alexei8a/Open-Air-duinoberry/Screenshots/device_list.png

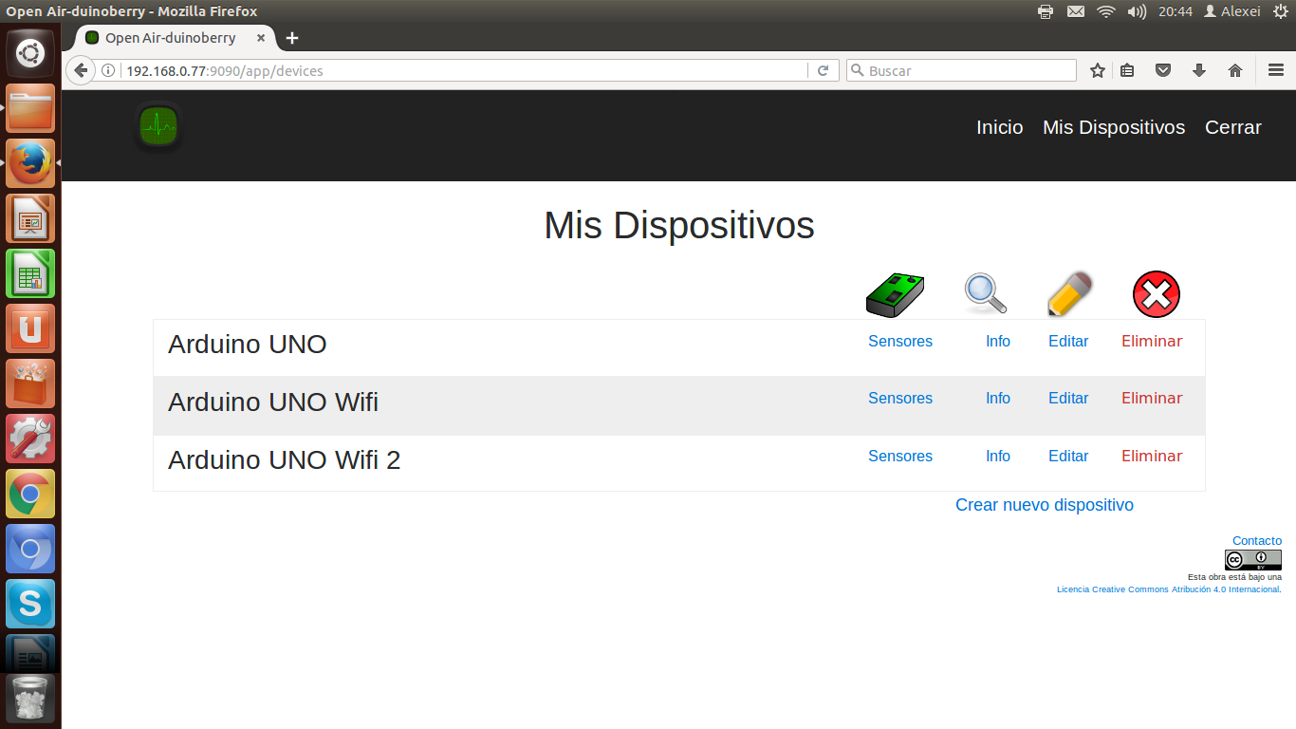
Screenshots/device_list.png
