alexei8a/Open-Air-duinoberry/Screenshots/edit_device.png

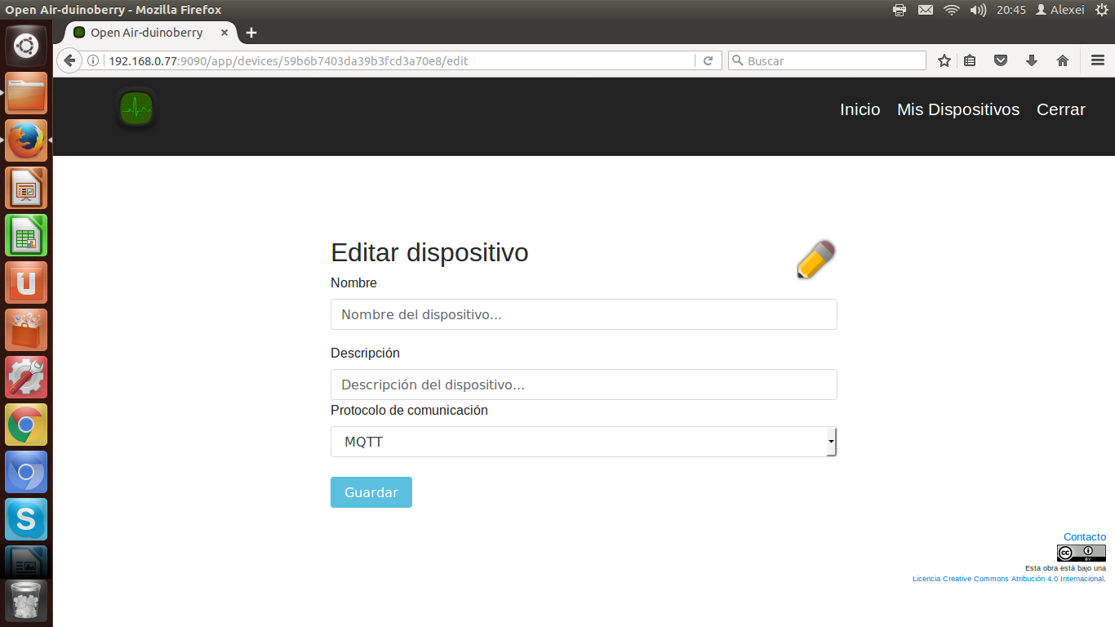
Screenshots/edit_device.png
