alexei8a/Open-Air-duinoberry/Screenshots/edit_sensor.png

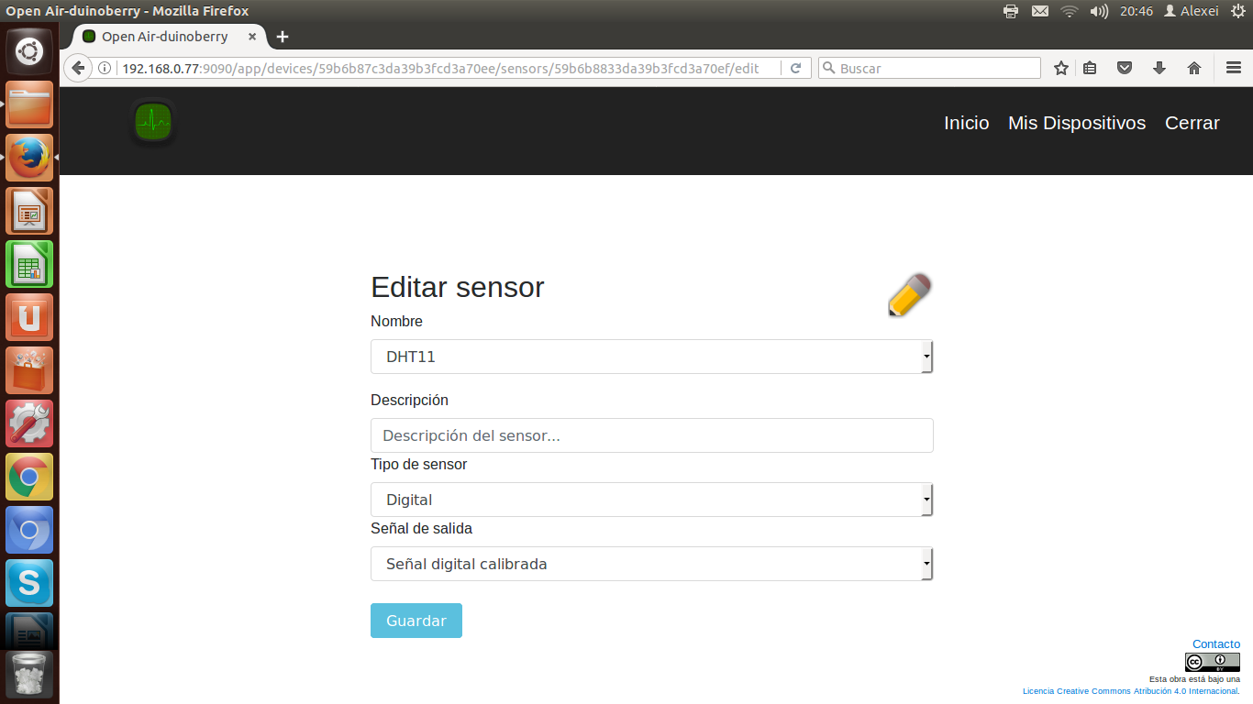
Screenshots/edit_sensor.png
