alexei8a/Open-Air-duinoberry/Screenshots/GPS_bb.png

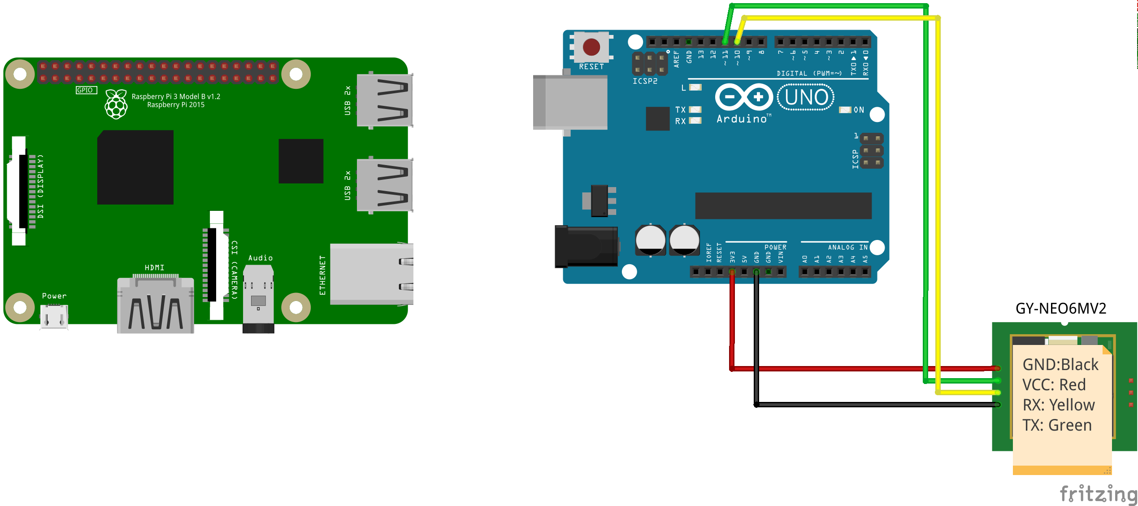
Screenshots/GPS_bb.png
