alexei8a/Open-Air-duinoberry/Screenshots/home.png

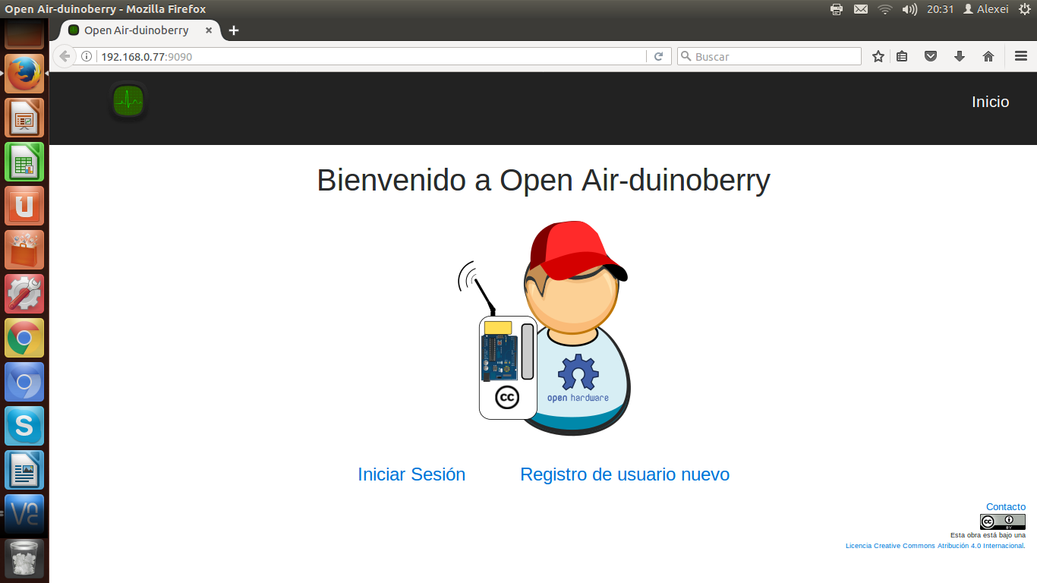
Screenshots/home.png
