alexei8a/Open-Air-duinoberry/Screenshots/Integración Airduino.png

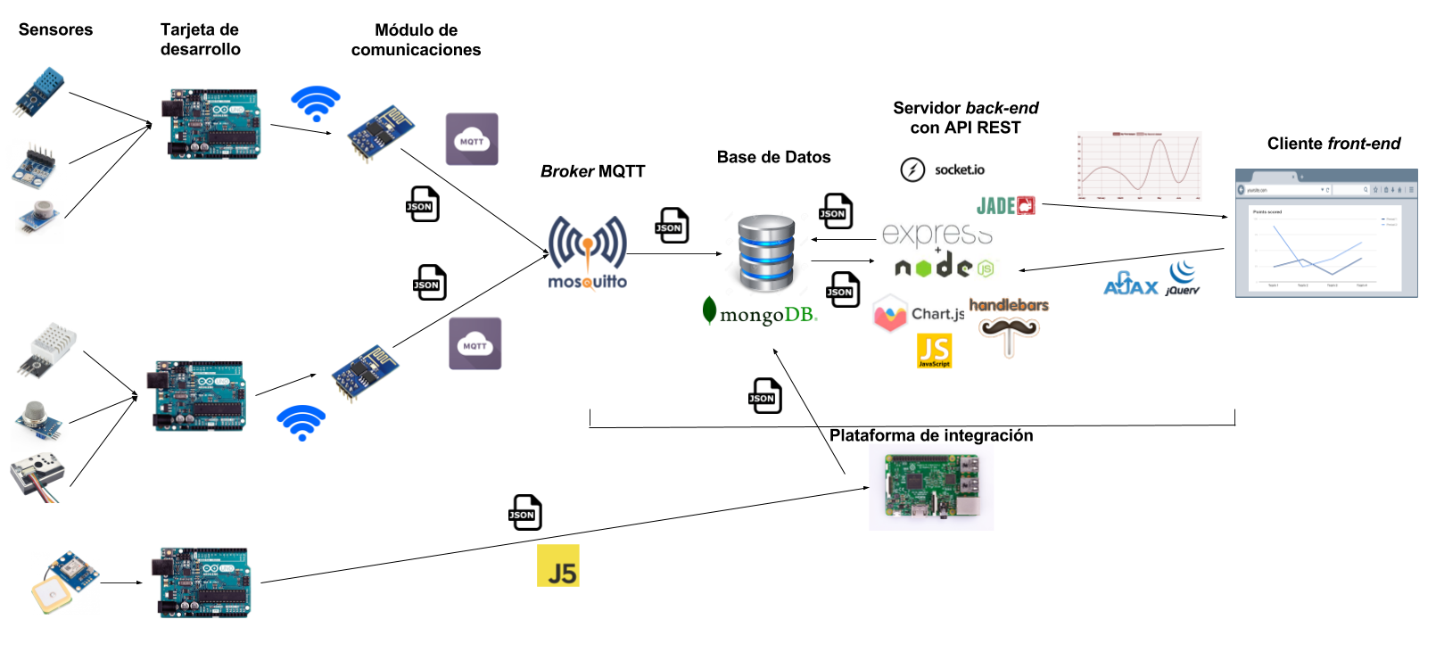
Screenshots/Integración Airduino.png
