alexei8a/Open-Air-duinoberry/Screenshots/MQ135_DHT22_GPY_bb.png

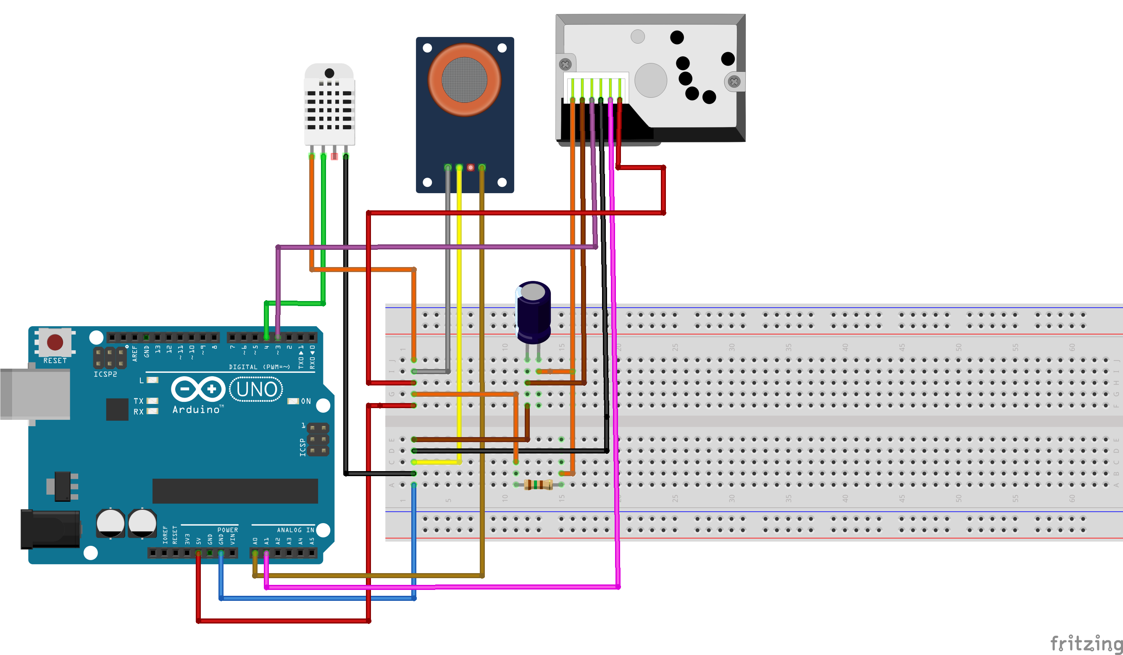
Screenshots/MQ135_DHT22_GPY_bb.png
