alexei8a/Open-Air-duinoberry/Screenshots/new_device.png

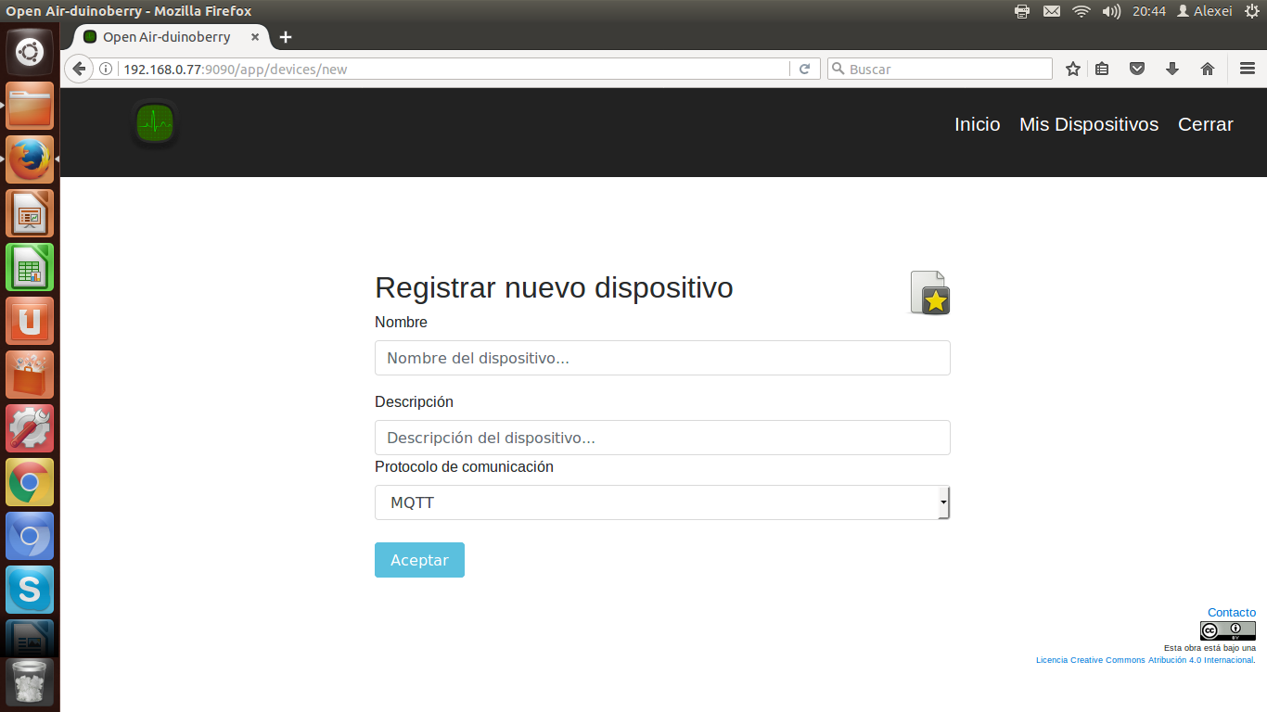
Screenshots/new_device.png
