alexei8a/Open-Air-duinoberry/Screenshots/new_pass.png

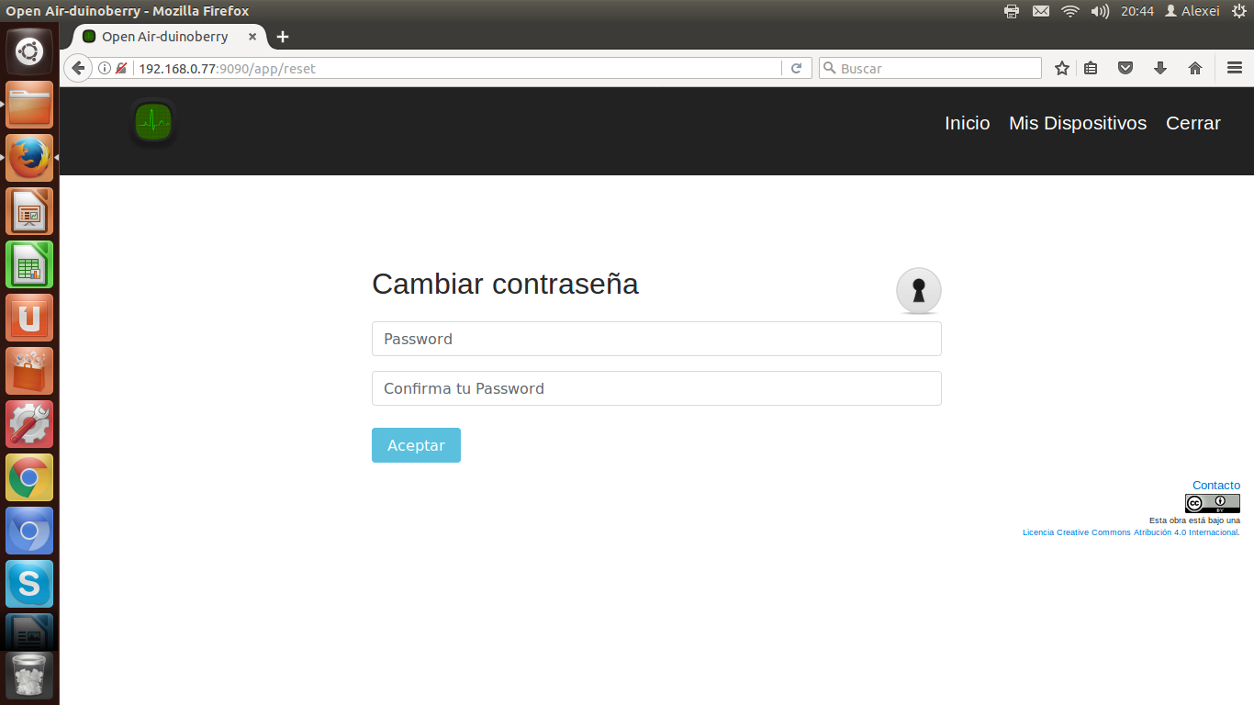
Screenshots/new_pass.png
