alexei8a/Open-Air-duinoberry/Screenshots/new_sensor.png

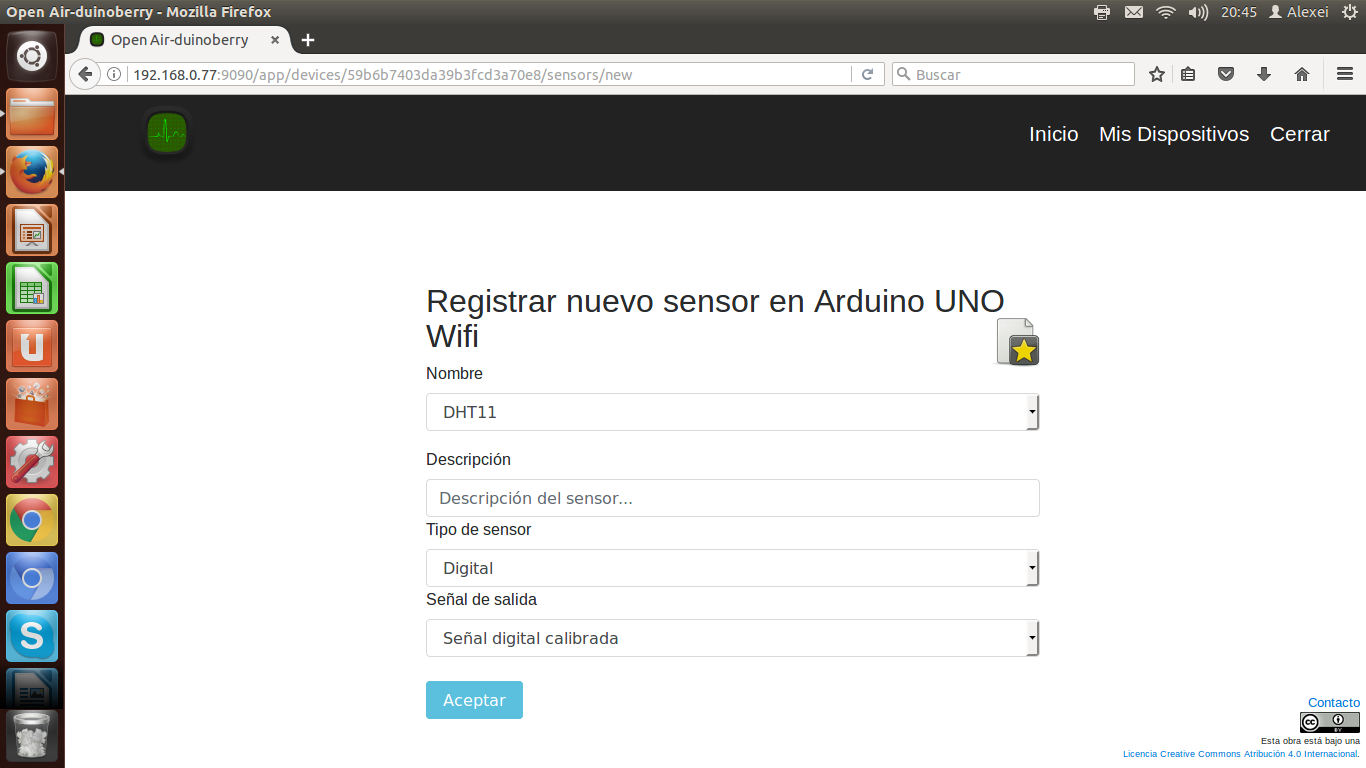
Screenshots/new_sensor.png
