alexei8a/Open-Air-duinoberry/Screenshots/password.png

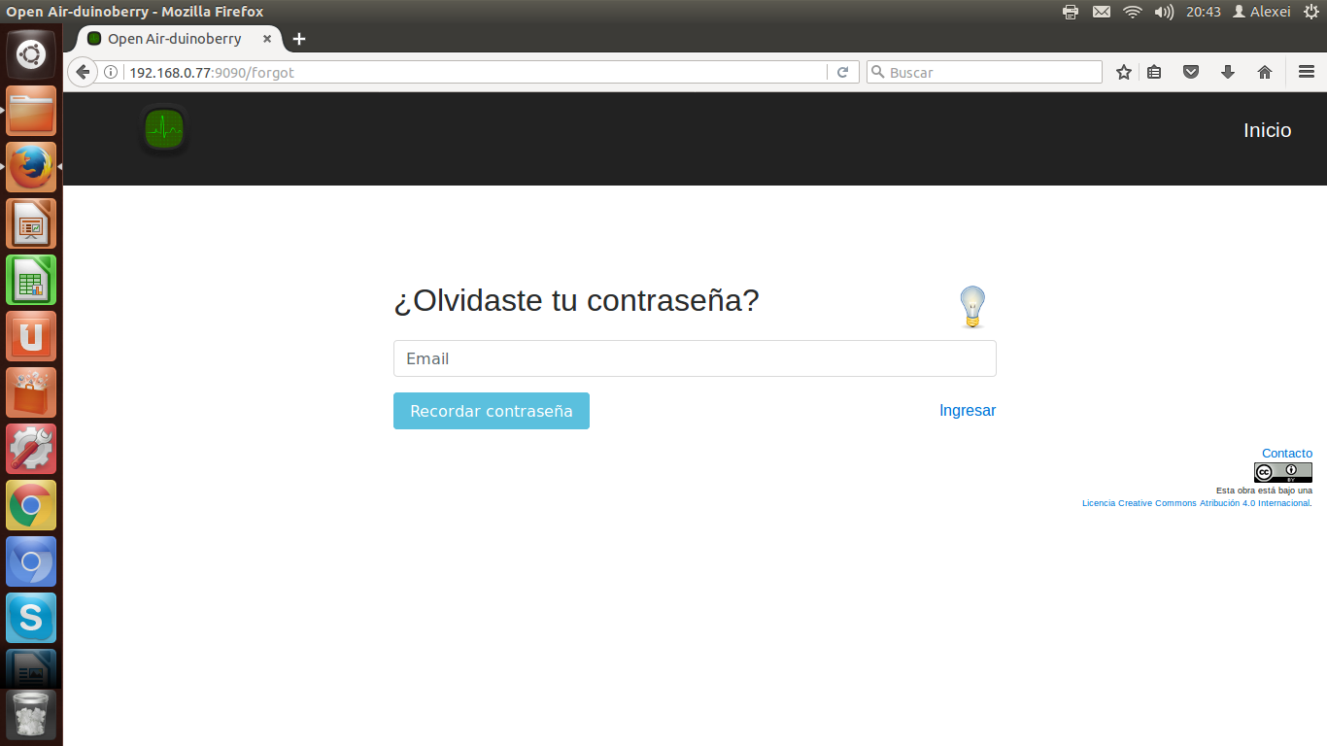
Screenshots/password.png
