alexei8a/Open-Air-duinoberry/Screenshots/sensor_list.png

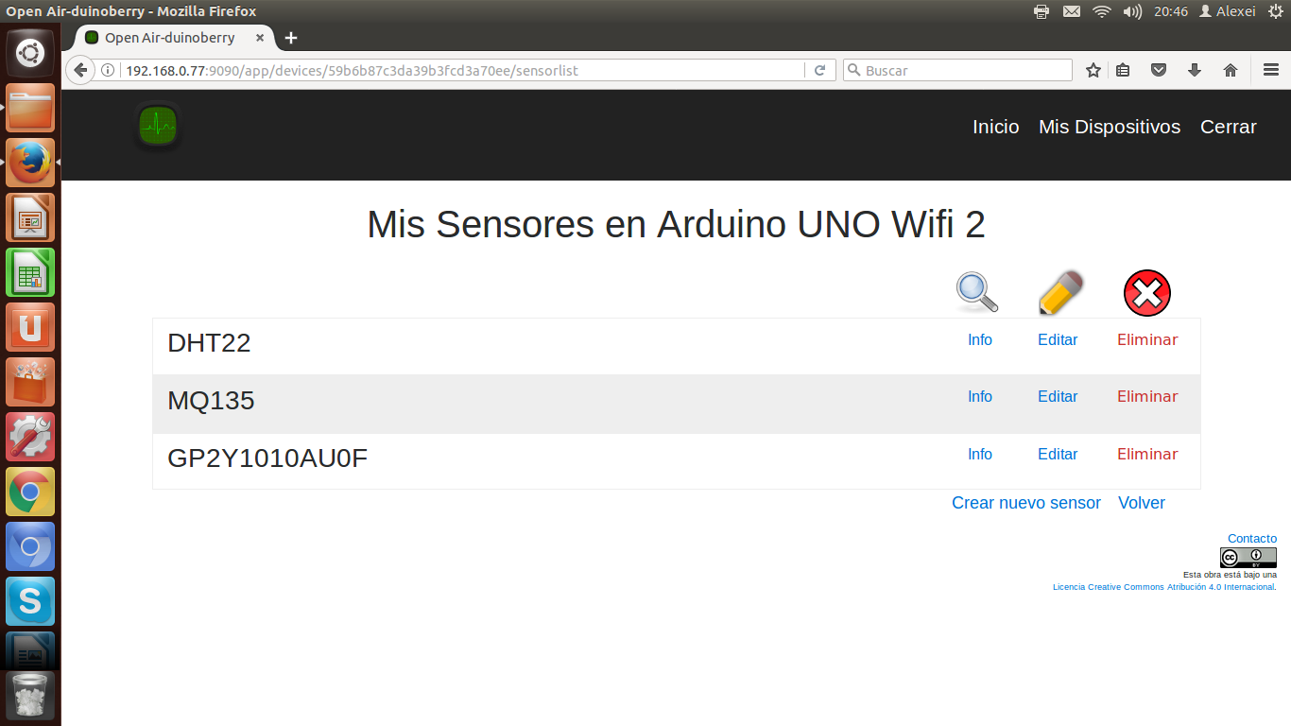
Screenshots/sensor_list.png
