alexei8a/Open-Air-duinoberry/Screenshots/sensores-terminal.png

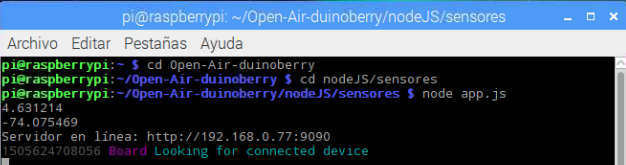
Screenshots/sensores-terminal.png
