alexei8a/Open-Air-duinoberry/Screenshots/sensors_home.png

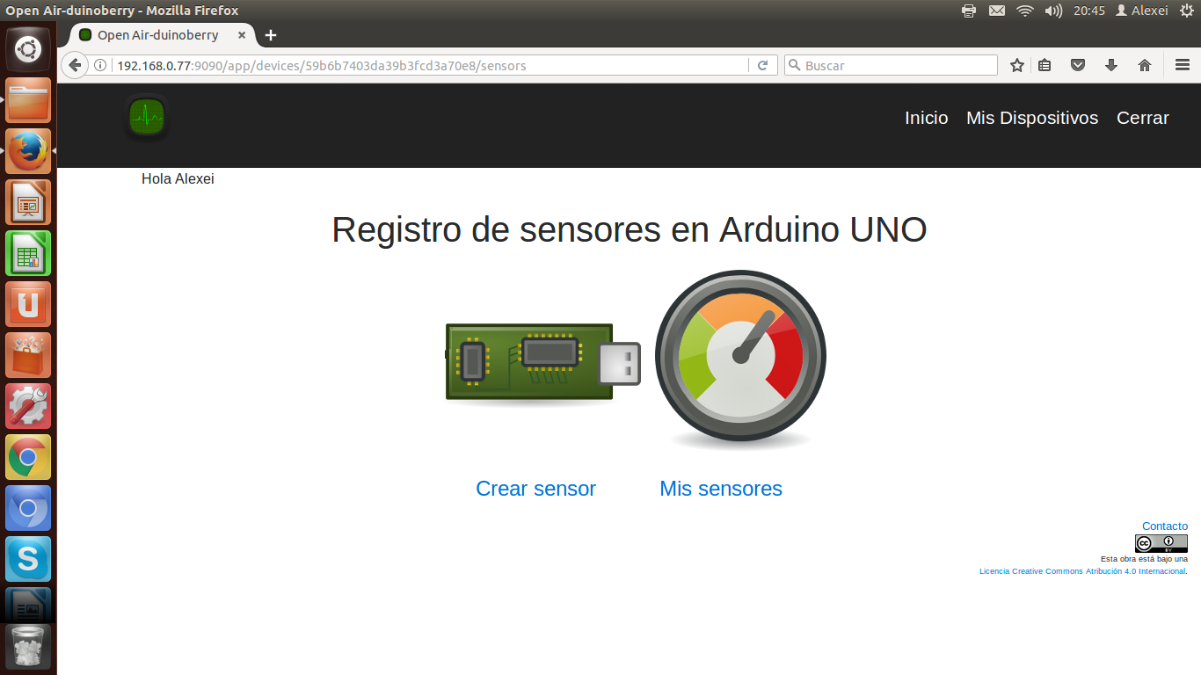
Screenshots/sensors_home.png
