alexei8a/Open-Air-duinoberry/Screenshots/signup.png

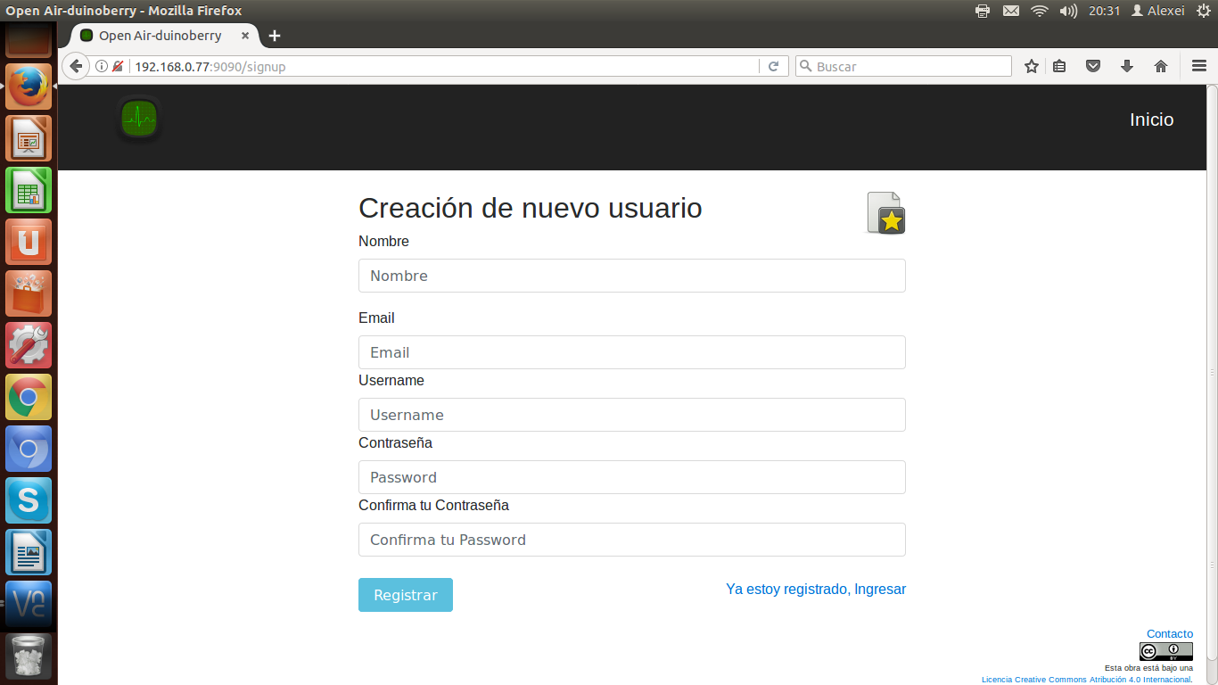
Screenshots/signup.png
