alexei8a/Open-Air-duinoberry/Screenshots/tabla.png

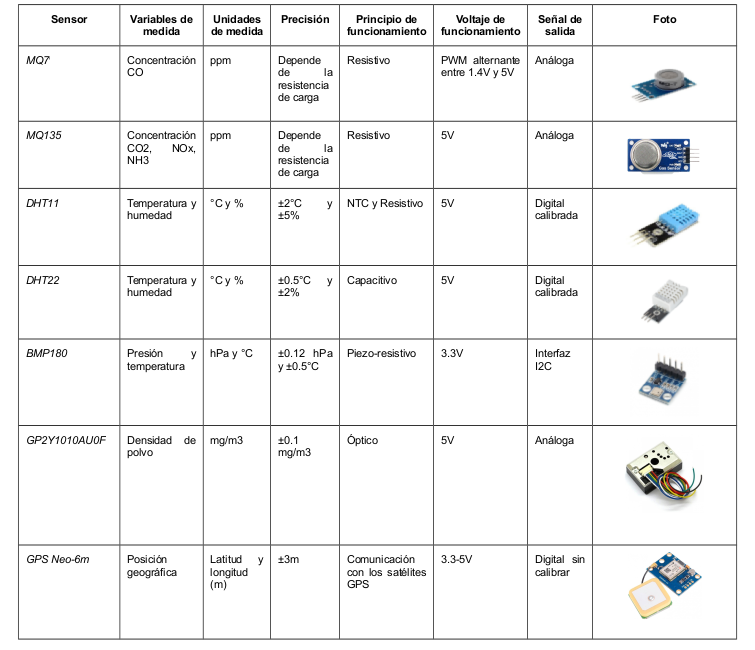
Screenshots/tabla.png
