alexei8a/Open-Air-duinoberry/Screenshots/visualiza_home.png

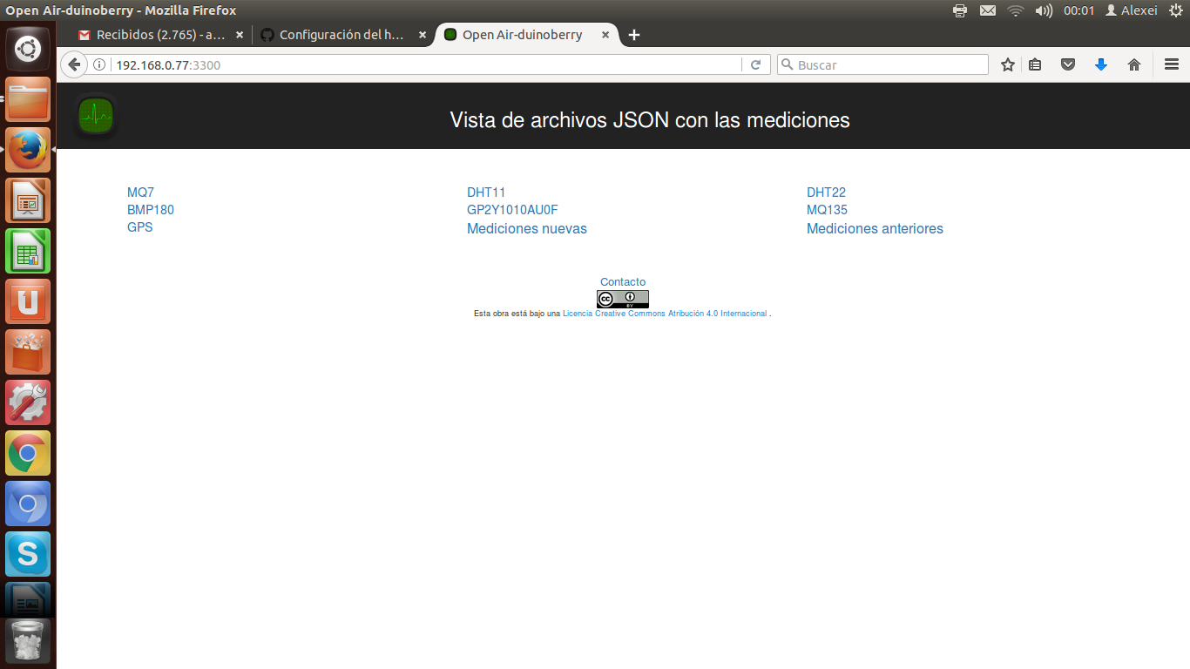
Screenshots/visualiza_home.png
