alexei8a/Open-Air-duinoberry/Screenshots/before_measures.png

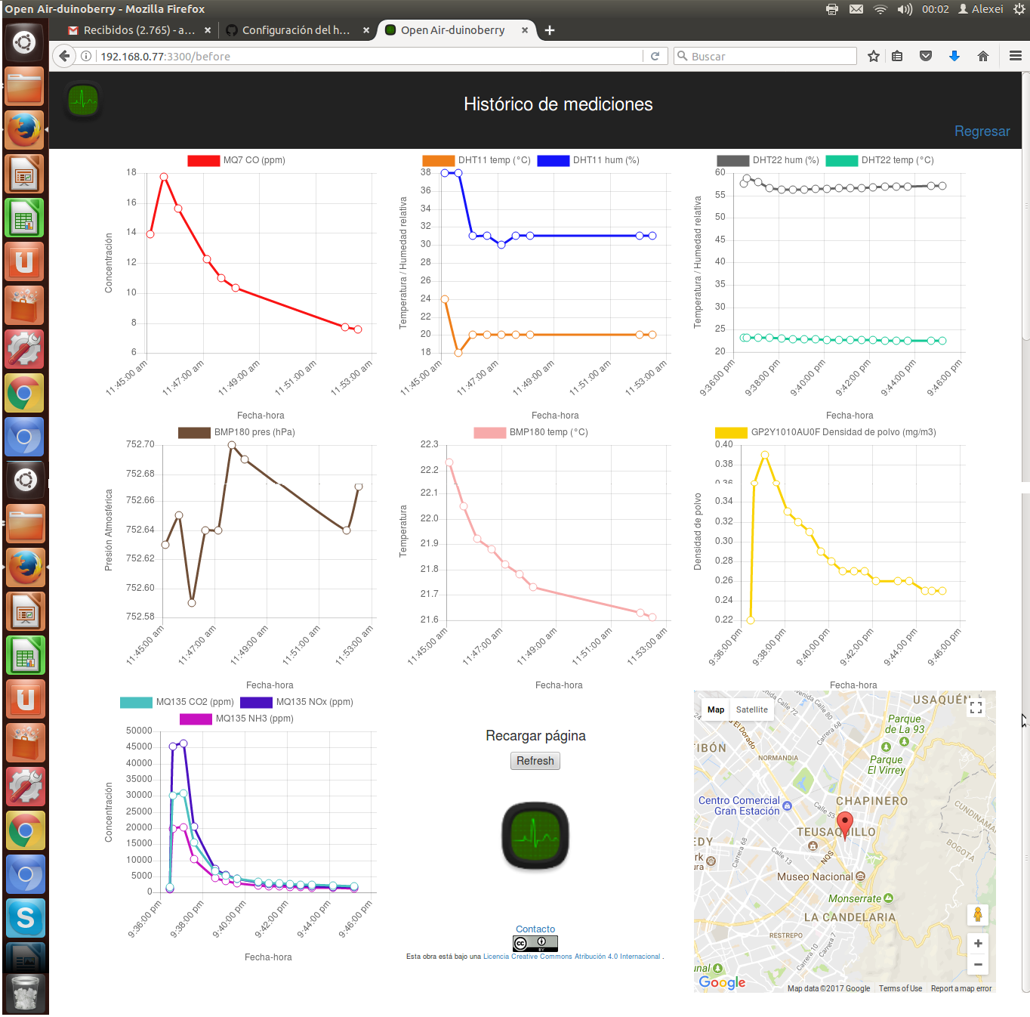
Screenshots/before_measures.png
