alexei8a/Open-Air-duinoberry/Screenshots/measures.png

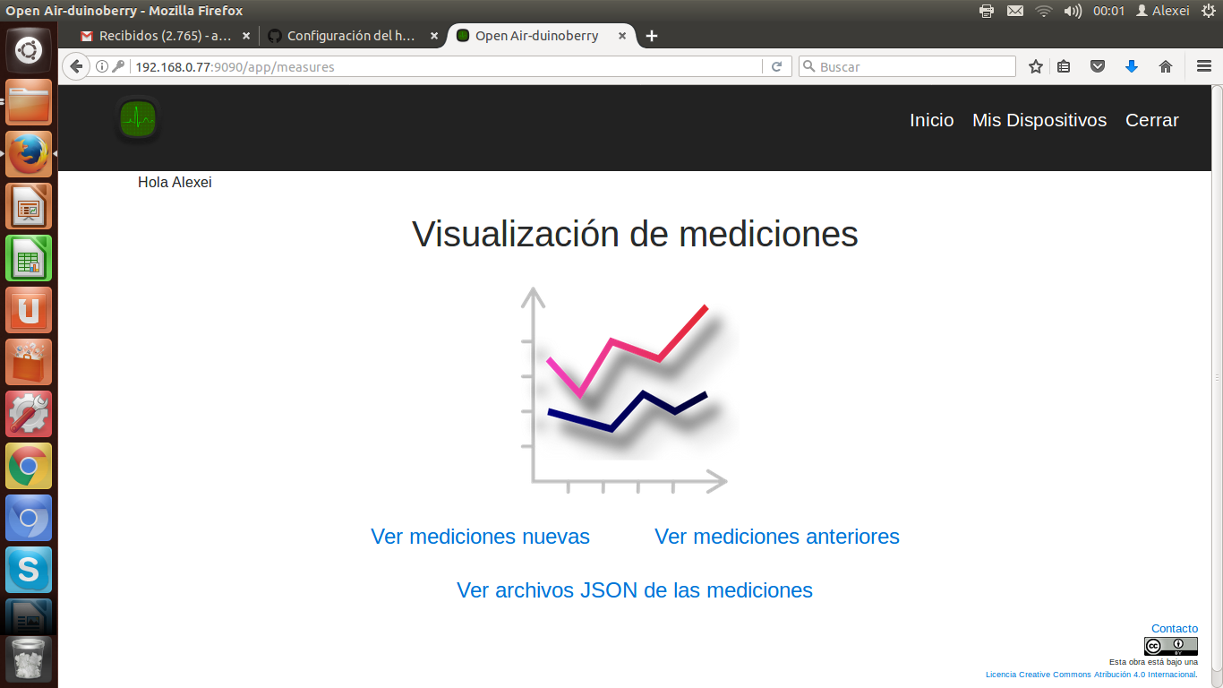
Screenshots/measures.png
