alexei8a/Open-Air-duinoberry/Screenshots/new_measures.png

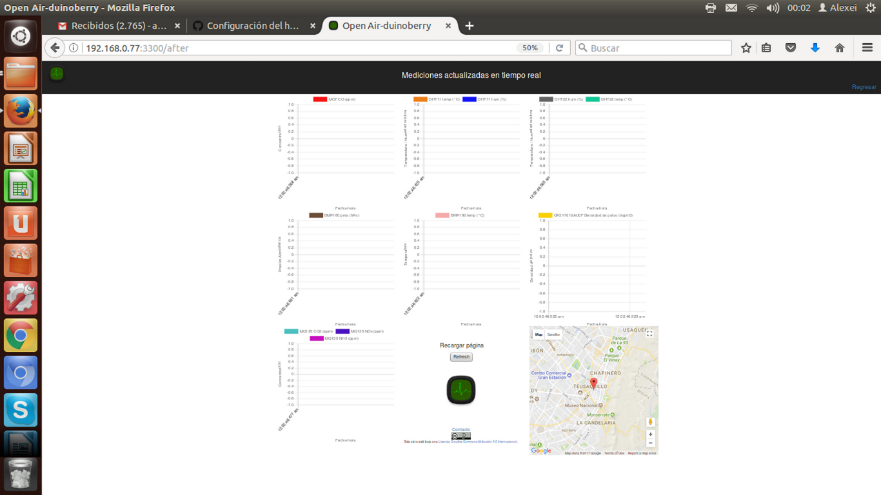
Screenshots/new_measures.png
